JN513/pico_coffee_roaster/include/motor.h

#ifndef __MOTOR_H__
#define __MOTOR_H__


/**
 * @brief 
 * 
 */
void init_motor();

/**
 * @brief Set the motor power object
 * 
 * @param percent 
 */
void set_motor_power(unsigned int percent);

#endif // !__MOTOR_H__
