JN513/pico_coffee_roaster/include/max31865.h

#ifndef MAX31865_H
#define MAX31865_H

#include <stdint.h>
#include <stdbool.h>
#include "hardware/spi.h"

// Estrutura do dispositivo
typedef struct {
    spi_inst_t *spi;
    uint cs_pin;
    uint rdy_pin;
    uint8_t config;
    float rref;
} max31865_t;

/**
 * @brief 
 * 
 * @param dev 
 * @param spi 
 * @param sck_pin 
 * @param mosi_pin 
 * @param miso_pin 
 * @param cs_pin 
 * @param rdy_pin 
 * @param rref_ohms 
 */
void max31865_init(
    max31865_t *dev,
    spi_inst_t *spi,
    uint sck_pin,
    uint mosi_pin,
    uint miso_pin,
    uint cs_pin,
    uint rdy_pin,
    float rref_ohms
);

/**
 * @brief 
 * 
 * @param dev 
 * @param temperature 
 * @return true 
 * @return false 
 */
bool max31865_read_celsius(max31865_t *dev, float *temperature);

#endif
